flupes/aaqim/test/epd_ada_gfx/B612Mono-Bold-18pt7b.h

const uint8_t B612Mono_Bold18pt7bBitmaps[] PROGMEM = {
  0x00, 0xFF, 0xFF, 0xFF, 0xFF, 0xFF, 0xFF, 0xFF, 0xFF, 0xFF, 0xFF, 0xE0,
  0x1D, 0xFF, 0xFD, 0xC0, 0xEF, 0xDF, 0xBF, 0x7E, 0xFD, 0xFB, 0x80, 0x0F,
  0x9F, 0x03, 0xE7, 0xC0, 0xF9, 0xF0, 0x3E, 0x7C, 0x0F, 0x1E, 0x03, 0xC7,
  0x80, 0xF1, 0xFF, 0xFF, 0xFF, 0xFF, 0xFF, 0xFF, 0xFF, 0xF1, 0xF3, 0xE0,
  0x7C, 0xF8, 0x1E, 0x3C, 0x07, 0x8F, 0x0F, 0xFF, 0xFF, 0xFF, 0xFF, 0xFF,
  0xFF, 0xCF, 0x9F, 0x03, 0xE7, 0xC0, 0xF9, 0xF0, 0x3C, 0x78, 0x0F, 0x1E,
  0x07, 0xC7, 0x80, 0x00, 0xC0, 0x0F, 0x80, 0x1F, 0x00, 0x3E, 0x01, 0xFF,
  0x87, 0xFF, 0x9F, 0xFF, 0x7D, 0xEC, 0xFB, 0xC1, 0xF7, 0x83, 0xEF, 0x07,
  0xFE, 0x07, 0xFC, 0x07, 0xFC, 0x03, 0xFE, 0x03, 0xFE, 0x07, 0xFC, 0x0F,
  0x7C, 0x1E, 0x78, 0x3C, 0xF0, 0x79, 0xEC, 0xF7, 0xDF, 0xFF, 0x7F, 0xFE,
  0xFF, 0xF0, 0x7F, 0xC0, 0x1F, 0x00, 0x3E, 0x00, 0x7C, 0x00, 0x3E, 0x1F,
  0x3F, 0x8F, 0x3F, 0xEF, 0x9E, 0xF7, 0x8F, 0x7F, 0xC7, 0xBF, 0xC3, 0xDF,
  0xE1, 0xEF, 0xE0, 0xFF, 0xF0, 0x3F, 0xF8, 0x07, 0x78, 0x00, 0x7F, 0xC0,
  0x3F, 0xF0, 0x3F, 0xFC, 0x1F, 0xDE, 0x1F, 0xEF, 0x0F, 0xF7, 0x8F, 0xFB,
  0xC7, 0xFD, 0xE7, 0xDF, 0xF3, 0xE7, 0xF3, 0xE1, 0xF0, 0x07, 0xE0, 0x03,
  0xFE, 0x01, 0xFF, 0xC0, 0xFF, 0xF0, 0x3E, 0x18, 0x0F, 0x82, 0x03, 0xE0,
  0x00, 0xFC, 0x00, 0x1F, 0x00, 0x07, 0xE0, 0x03, 0xF8, 0x01, 0xFF, 0x01,
  0x7F, 0xE7, 0xBE, 0xF9, 0xEF, 0xBF, 0x7B, 0xE7, 0xFE, 0xF8, 0xFF, 0xBE,
  0x3F, 0xCF, 0x87, 0xF1, 0xFF, 0xF8, 0x3F, 0xFF, 0x07, 0xFF, 0xE0, 0xFC,
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
  {  1309,  16,  23,  20,    2,  -22 },   // 0x46 'F'
  {  1355,  18,  23,  20,    1,  -22 },   // 0x47 'G'
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

const GFXfont B612Mono_Bold18pt7b PROGMEM = {
  (uint8_t  *)B612Mono_Bold18pt7bBitmaps,
  (GFXglyph *)B612Mono_Bold18pt7bGlyphs,
  0x20, 0x7E, 36 };

// Approx. 4356 bytes
