flupes/aaqim/test/epd_ada_gfx/B612Mono-Bold-48pt7b.h

const uint8_t B612Mono_Bold48pt7bBitmaps[] PROGMEM = {
  0x00, 0xFF, 0xF7, 0xFF, 0xBF, 0xFD, 0xFF, 0xEF, 0xFF, 0x7F, 0xFB, 0xFF,
  0xDF, 0xFE, 0xFF, 0xF7, 0xFF, 0xBF, 0xFD, 0xFF, 0xEF, 0xFF, 0x7F, 0xFB,
  0xFF, 0xDF, 0xFE, 0xFF, 0xF7, 0xFF, 0xBF, 0xFD, 0xFF, 0xEF, 0xFF, 0x7F,
  0xFB, 0xFF, 0xDF, 0xFE, 0xFF, 0xF7, 0xFF, 0xBF, 0xFD, 0xFF, 0xEF, 0xFF,
  0x7F, 0xFB, 0xFF, 0xDF, 0xFE, 0xFF, 0xF7, 0xFF, 0xBF, 0xFD, 0xFF, 0xEF,
  0xFF, 0x7F, 0xFB, 0xFF, 0xDF, 0xFE, 0xFF, 0xF7, 0xFF, 0xBF, 0xE1, 0xC0,
  0x00, 0x00, 0x00, 0x00, 0x00, 0x01, 0xF0, 0x3F, 0xC1, 0xFF, 0x1F, 0xFD,
  0xFF, 0xFF, 0xFF, 0xFF, 0xFF, 0xFF, 0xFF, 0xFF, 0xFF, 0xFB, 0xFF, 0x8F,
  0xF8, 0x3F, 0x80, 0xF8, 0x00, 0xFF, 0xCF, 0xFF, 0xFF, 0x3F, 0xFF, 0xFC,
  0xFF, 0xFF, 0xF3, 0xFF, 0xFF, 0xCF, 0xFF, 0xFF, 0x3F, 0xFF, 0xFC, 0xFF,
  0xFF, 0xF3, 0xFF, 0xFF, 0xCF, 0xFF, 0xFF, 0x3F, 0xFF, 0xFC, 0xFF, 0xFF,
  0xF3, 0xFF, 0xFF, 0xCF, 0xFF, 0xFF, 0x3F, 0xF7, 0xF8, 0x7F, 0x9F, 0xE1,
  0xFE, 0x7F, 0x87, 0xF9, 0xFE, 0x1F, 0xE7, 0xF8, 0x7F, 0x80, 0x00, 0x00,
  0x1F, 0x00, 0x01, 0xE0, 0x00, 0x0F, 0xFF, 0x80, 0xFF, 0xF0, 0x00, 0x07,
  0xFF, 0xC0, 0x7F, 0xF8, 0x00, 0x03, 0xFF, 0xE0, 0x3F, 0xFC, 0x00, 0x01,
  0xFF, 0xF0, 0x1F, 0xFE, 0x00, 0x00, 0xFF, 0xF8, 0x1F, 0xFF, 0x00, 0x00,
  0x7F, 0xFC, 0x0F, 0xFF, 0x80, 0x00, 0x3F, 0xFE, 0x07, 0xFF, 0x80, 0x00,
  0x1F, 0xFE, 0x03, 0xFF, 0xC0, 0x00, 0x0F, 0xFF, 0x01, 0xFF, 0xE0, 0x00,
  0x07, 0xFF, 0x80, 0xFF, 0xF0, 0x00, 0x03, 0xFF, 0xC0, 0x7F, 0xF8, 0x00,
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
  {  9322,  40,  60,  52,    7,  -59 },   // 0x46 'F'
  {  9622,  48,  62,  52,    2,  -60 },   // 0x47 'G'
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

const GFXfont B612Mono_Bold48pt7b PROGMEM = {
  (uint8_t  *)B612Mono_Bold48pt7bBitmaps,
  (GFXglyph *)B612Mono_Bold48pt7bGlyphs,
  0x20, 0x7E, 97 };

// Approx. 26715 bytes
