flupes/aaqim/test/epd_ada_gfx/ClearSans-Bold-48pt7b.h

const uint8_t ClearSans_Bold48pt7bBitmaps[] PROGMEM = {
  0x00, 0x7F, 0xF3, 0xFF, 0x9F, 0xFC, 0xFF, 0xE7, 0xFE, 0x3F, 0xF1, 0xFF,
  0x8F, 0xFC, 0x7F, 0xE3, 0xFF, 0x1F, 0xF8, 0xFF, 0xC7, 0xFE, 0x3F, 0xF1,
  0xFF, 0x8F, 0xFC, 0x7F, 0xE3, 0xFF, 0x1F, 0xF8, 0xFF, 0xC7, 0xFE, 0x3F,
  0xF0, 0xFF, 0x87, 0xFC, 0x3F, 0xE1, 0xFF, 0x0F, 0xF8, 0x7F, 0xC3, 0xFE,
  0x1F, 0xF0, 0xFF, 0x87, 0xFC, 0x3F, 0xE1, 0xFF, 0x0F, 0xF0, 0x7F, 0x80,
  0x00, 0x00, 0x00, 0x00, 0x00, 0x00, 0x00, 0x00, 0x00, 0x07, 0xF0, 0xFF,
  0xC7, 0xFF, 0x7F, 0xFB, 0xFF, 0xFF, 0xFF, 0xFF, 0xFF, 0xFF, 0xFF, 0xFC,
  0xFF, 0xE7, 0xFE, 0x0F, 0xE0, 0xFF, 0xE0, 0x7F, 0xFF, 0xFE, 0x07, 0xFF,
  0xFF, 0xE0, 0x7F, 0xF7, 0xFE, 0x03, 0xFF, 0x7F, 0xE0, 0x3F, 0xF7, 0xFE,
  0x03, 0xFF, 0x7F, 0xE0, 0x3F, 0xF7, 0xFC, 0x03, 0xFE, 0x7F, 0xC0, 0x3F,
  0xE7, 0xFC, 0x03, 0xFE, 0x7F, 0xC0, 0x3F, 0xE7, 0xFC, 0x03, 0xFE, 0x7F,
  0xC0, 0x3F, 0xE7, 0xFC, 0x03, 0xFE, 0x7F, 0xC0, 0x3F, 0xE7, 0xFC, 0x03,
  0xFE, 0x7F, 0xC0, 0x3F, 0xE3, 0xFC, 0x01, 0xFE, 0x3F, 0xC0, 0x1F, 0xE3,
  0xFC, 0x01, 0xFE, 0x3F, 0xC0, 0x1F, 0xE3, 0xF8, 0x01, 0xFC, 0x3F, 0x80,
  0x1F, 0xC3, 0xF8, 0x01, 0xFC, 0x00, 0x00, 0x1F, 0xE0, 0x0F, 0xF0, 0x00,
  0x00, 0x0F, 0xF0, 0x07, 0xF8, 0x00, 0x00, 0x07, 0xF0, 0x03, 0xF8, 0x00,
  0x00, 0x03, 0xF8, 0x01, 0xFC, 0x00, 0x00, 0x03, 0xFC, 0x01, 0xFE, 0x00,
  0x00, 0x01, 0xFE, 0x00, 0xFF, 0x00, 0x00, 0x00, 0xFE, 0x00, 0x7F, 0x00,
  0x00, 0x00, 0xFF, 0x00, 0x7F, 0x80, 0x00, 0x00, 0x7F, 0x80, 0x3F, 0xC0,
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
  {  8886,  35,  54,  43,    6,  -53 },   // 0x46 'F'
  {  9123,  46,  56,  55,    4,  -54 },   // 0x47 'G'
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

const GFXfont ClearSans_Bold48pt7b PROGMEM = {
  (uint8_t  *)ClearSans_Bold48pt7bBitmaps,
  (GFXglyph *)ClearSans_Bold48pt7bGlyphs,
  0x20, 0x7E, 108 };

// Approx. 23077 bytes
