flupes/aaqim/test/epd_ada_gfx/Hack-Bold-18pt7b.h

const uint8_t Hack_Bold18pt7bBitmaps[] PROGMEM = {
  0x00, 0x79, 0xE7, 0x9E, 0x79, 0xE7, 0x9E, 0x79, 0xE7, 0x8E, 0x30, 0xC3,
  0x00, 0x00, 0x07, 0x9E, 0xFD, 0xE7, 0x80, 0xF0, 0xFF, 0x0F, 0xF0, 0xFF,
  0x0F, 0xF0, 0xFF, 0x0F, 0xF0, 0xFF, 0x0F, 0x01, 0xC7, 0x80, 0x71, 0xC0,
  0x3C, 0x70, 0x0E, 0x3C, 0x03, 0x8E, 0x0F, 0xFF, 0xF3, 0xFF, 0xFC, 0xFF,
  0xFF, 0x3F, 0xFF, 0xC1, 0xC7, 0x00, 0xF1, 0xC0, 0x38, 0xF0, 0x0E, 0x38,
  0x3F, 0xFF, 0xCF, 0xFF, 0xF3, 0xFF, 0xFC, 0xFF, 0xFF, 0x07, 0x1C, 0x01,
  0xC7, 0x00, 0xF1, 0xC0, 0x38, 0xF0, 0x0E, 0x38, 0x00, 0x03, 0x80, 0x0E,
  0x00, 0x38, 0x00, 0xE0, 0x1F, 0xF8, 0xFF, 0xE7, 0xFF, 0x9E, 0xC6, 0xF3,
  0x03, 0xCC, 0x0F, 0xB0, 0x1F, 0xC0, 0x7F, 0xE0, 0xFF, 0xC0, 0xFF, 0x80,
  0xFF, 0x03, 0x3C, 0x0C, 0xF8, 0x33, 0xD8, 0xDF, 0x7F, 0xF9, 0xFF, 0xE7,
  0xFF, 0x01, 0xE0, 0x03, 0x80, 0x0E, 0x00, 0x38, 0x00, 0xE0, 0x1E, 0x00,
  0x0F, 0xE0, 0x07, 0xF8, 0x01, 0xC7, 0x00, 0xE1, 0xC0, 0x1C, 0x70, 0x07,
  0xF8, 0x08, 0xFE, 0x1E, 0x1E, 0x1E, 0x00, 0x3E, 0x00, 0x3C, 0x00, 0x78,
  0x78, 0x78, 0x3F, 0x10, 0x1F, 0xE0, 0x07, 0x3C, 0x01, 0x87, 0x00, 0xE1,
  0xC0, 0x1C, 0x70, 0x07, 0xF8, 0x00, 0xFE, 0x00, 0x1E, 0x00, 0x07, 0xF0,
  0x07, 0xFC, 0x07, 0xFE, 0x07, 0xFF, 0x03, 0xC0, 0x81, 0xE0, 0x00, 0x78,
  0x00, 0x3C, 0x00, 0x1F, 0x00, 0x0F, 0xC0, 0x1F, 0xF0, 0x0F, 0x78, 0xFF,
  0x3E, 0x7F, 0x8F, 0xBF, 0xC3, 0xDD, 0xE1, 0xFE, 0xF0, 0x7F, 0x7C, 0x1F,
  0x3F, 0xFF, 0x8F, 0xFF, 0xE3, 0xFF, 0xF0, 0x7E, 0x7C, 0xFF, 0xFF, 0xFF,
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
  {  1224,  13,  22,  18,    3,  -21 },   // 0x46 'F'
  {  1260,  15,  22,  18,    2,  -21 },   // 0x47 'G'
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

const GFXfont Hack_Bold18pt7b PROGMEM = {
  (uint8_t  *)Hack_Bold18pt7bBitmaps,
  (GFXglyph *)Hack_Bold18pt7bGlyphs,
  0x20, 0x7E, 35 };

// Approx. 4046 bytes
