flupes/aaqim/test/epd_ada_gfx/Hack-Bold-48pt7b.h

const uint8_t Hack_Bold48pt7bBitmaps[] PROGMEM = {
  0x00, 0x7F, 0xF9, 0xFF, 0xE7, 0xFF, 0x9F, 0xFE, 0x7F, 0xF9, 0xFF, 0xE7,
  0xFF, 0x9F, 0xFE, 0x7F, 0xF9, 0xFF, 0xE7, 0xFF, 0x9F, 0xFE, 0x7F, 0xF9,
  0xFF, 0xE7, 0xFF, 0x9F, 0xFE, 0x7F, 0xF9, 0xFF, 0xE7, 0xFF, 0x0F, 0xFC,
  0x3F, 0xF0, 0xFF, 0xC3, 0xFF, 0x0F, 0xFC, 0x3F, 0xF0, 0xFF, 0xC1, 0xFE,
  0x07, 0xF8, 0x1F, 0xE0, 0x7F, 0x81, 0xFE, 0x07, 0xF8, 0x1F, 0xE0, 0x3F,
  0x80, 0xFE, 0x03, 0xF0, 0x0F, 0xC0, 0x3F, 0x00, 0xFC, 0x03, 0xF0, 0x00,
  0x00, 0x00, 0x00, 0x00, 0x00, 0x00, 0x00, 0x00, 0x00, 0x00, 0x00, 0x03,
  0xF0, 0x1F, 0xE0, 0xFF, 0xC7, 0xFF, 0x9F, 0xFE, 0xFF, 0xFF, 0xFF, 0xFF,
  0xFF, 0xFF, 0xFF, 0x7F, 0xF9, 0xFF, 0xE3, 0xFF, 0x07, 0xF8, 0x0F, 0xC0,
  0xFF, 0xC0, 0x0F, 0xFF, 0xFF, 0x00, 0x3F, 0xFF, 0xFC, 0x00, 0xFF, 0xFF,
  0xF0, 0x03, 0xFF, 0xFF, 0xC0, 0x0F, 0xFF, 0xFF, 0x00, 0x3F, 0xFF, 0xFC,
  0x00, 0xFF, 0xFF, 0xF0, 0x03, 0xFF, 0xFF, 0xC0, 0x0F, 0xFF, 0xFF, 0x00,
  0x3F, 0xFF, 0xFC, 0x00, 0xFF, 0xFF, 0xF0, 0x03, 0xFF, 0xFF, 0xC0, 0x0F,
  0xFF, 0xFF, 0x00, 0x3F, 0xFF, 0xFC, 0x00, 0xFF, 0xFF, 0xF0, 0x03, 0xFF,
  0xFF, 0xC0, 0x0F, 0xFF, 0xFF, 0x00, 0x3F, 0xFF, 0xFC, 0x00, 0xFF, 0xFF,
  0xF0, 0x03, 0xFF, 0xFF, 0xC0, 0x0F, 0xFF, 0xFF, 0x00, 0x3F, 0xF0, 0x00,
  0x00, 0x1F, 0xF0, 0x1F, 0xF0, 0x00, 0x00, 0x1F, 0xE0, 0x1F, 0xF0, 0x00,
  0x00, 0x3F, 0xE0, 0x1F, 0xF0, 0x00, 0x00, 0x3F, 0xE0, 0x1F, 0xE0, 0x00,
  0x00, 0x3F, 0xE0, 0x3F, 0xE0, 0x00, 0x00, 0x3F, 0xC0, 0x3F, 0xE0, 0x00,
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
  {  8649,  36,  59,  48,    7,  -58 },   // 0x46 'F'
  {  8915,  39,  61,  48,    5,  -59 },   // 0x47 'G'
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

const GFXfont Hack_Bold48pt7b PROGMEM = {
  (uint8_t  *)Hack_Bold48pt7bBitmaps,
  (GFXglyph *)Hack_Bold48pt7bGlyphs,
  0x20, 0x7E, 93 };

// Approx. 24315 bytes
