flupes/aaqim/src/graph_samples.h

#ifndef AAQIM_GRAPH_SAMPLES_H
#define AAQIM_GRAPH_SAMPLES_H

#include "display_samples.h"

class GFXcanvas1;

constexpr int16_t kGraphWidth = 144;
constexpr int16_t kGraphHeight = 100;

class GraphSamples : public DisplaySamples<kGraphWidth, int16_t> {
 public:
  GraphSamples(uint32_t period_in_seconds)
      : DisplaySamples(period_in_seconds) {}

  void Draw(GFXcanvas1 *black, GFXcanvas1 *red);

 protected:
  GFXcanvas1 *blackCanvas_;
  GFXcanvas1 *redCanvas_;
  const int16_t vStep_ = 100;
  int16_t lowerLimit_;
  int16_t upperLimit_;
  int16_t ValueToVerticalPixel(int16_t value);
  void Background();
  void Labels();
  void Serie();
  void Grid();
};

#endif
